euphi/ESP-LEDCtrl/src/buildnumber.h

/*
 * buildnumber.h
 *
 *  Created on: 15.05.2017
 *      Author: ian
 */

#ifndef SRC_BUILDNUMBER_H_
#define SRC_BUILDNUMBER_H_


//TODO: Implement auto-increment, e.g. with platformio

#define BUILD_NUMBER "4"
#define COMMIT_COUNTER "3"


#endif /* SRC_BUILDNUMBER_H_ */
